Lemontea-1/onnecting-rod-fixture/09_装配体/装配体.STEP

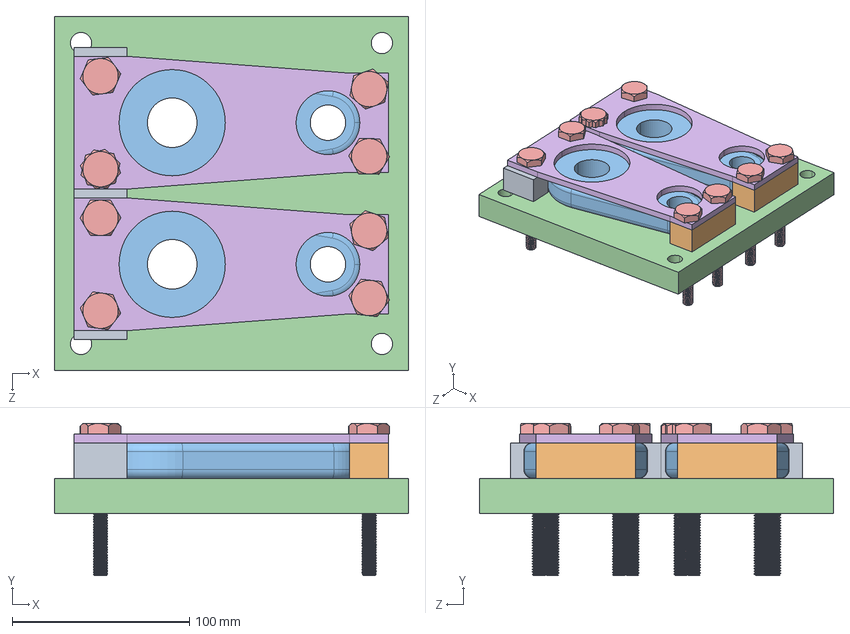
[picture p15: CAD file, 2026-06-10]
09_装配体/装配体.STEP
200.0 x 86.0 x 200.0 mm
V型定位块 x 2
V型小块 x 2
连杆零件图 x 2
底座(2)
螺栓(2) x 9
压力盖 x 2
