Lemontea-1/onnecting-rod-fixture/09_装配体/压力盖.STEP

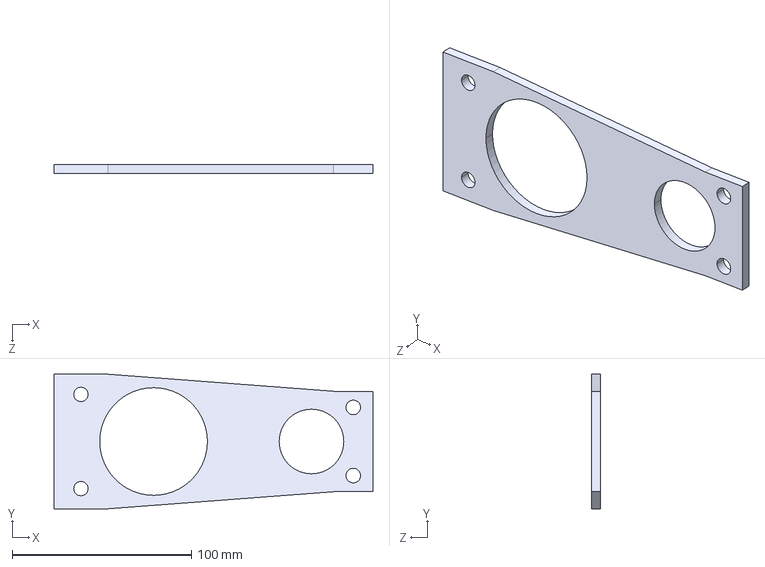
[picture p16: CAD file, 2026-06-09]
09_装配体/压力盖.STEP
177.8 x 75.0 x 5.00 mm
