Lemontea-1/onnecting-rod-fixture/09_装配体/最终装配体.SLDASM

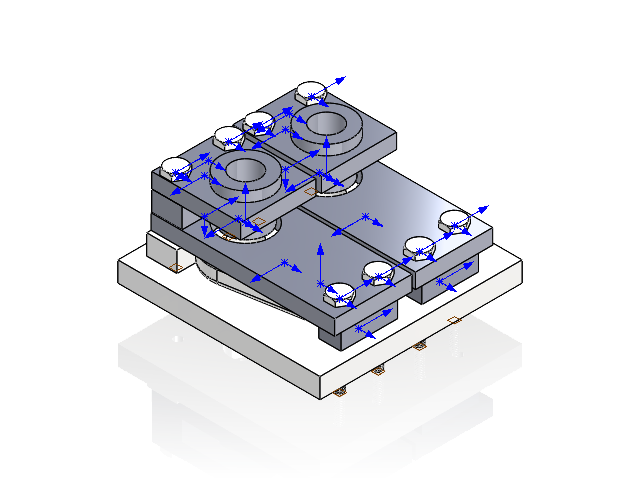
[picture p17: CAD file, 2026-06-10]
09_装配体/最终装配体.SLDASM
底座(2)
连杆零件图 x 2
V型定位块 x 2
压力盖 x 2
引导套筒组件（横向） x 2
套筒 x 2
螺栓(2) x 8
v型小块.step x 2
引导套筒组件（纵向) x 2
