Lemontea-1/onnecting-rod-fixture/06_钻套/装配体2.SLDASM

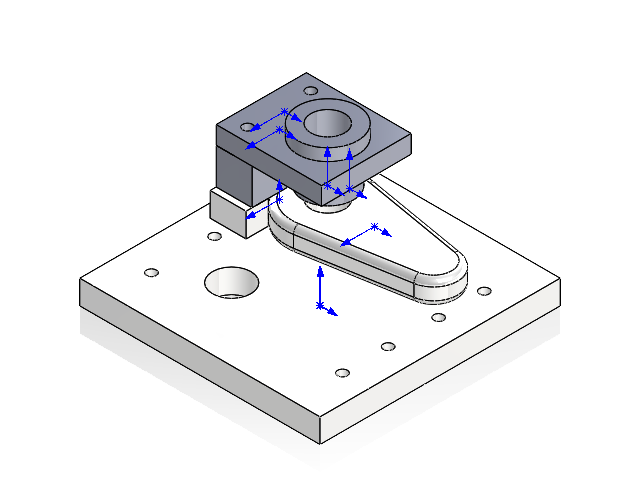
[picture p18: CAD file, 2026-06-10]
06_钻套/装配体2.SLDASM
引导套筒组件（横向）
引导套筒组件（纵向)
底座(2)
连杆零件图
V型定位块
套筒1
